jhpieper/marble-run/stl/straight-110.stl

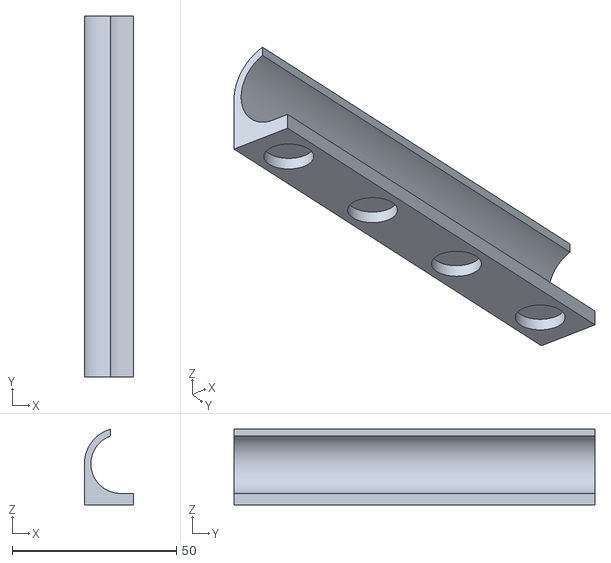
[picture p31: CAD file, 2020-05-29]
stl/straight-110.stl
15.0 x 110.0 x 23.1
