jhpieper/marble-run/stl/wheel-40-6.stl

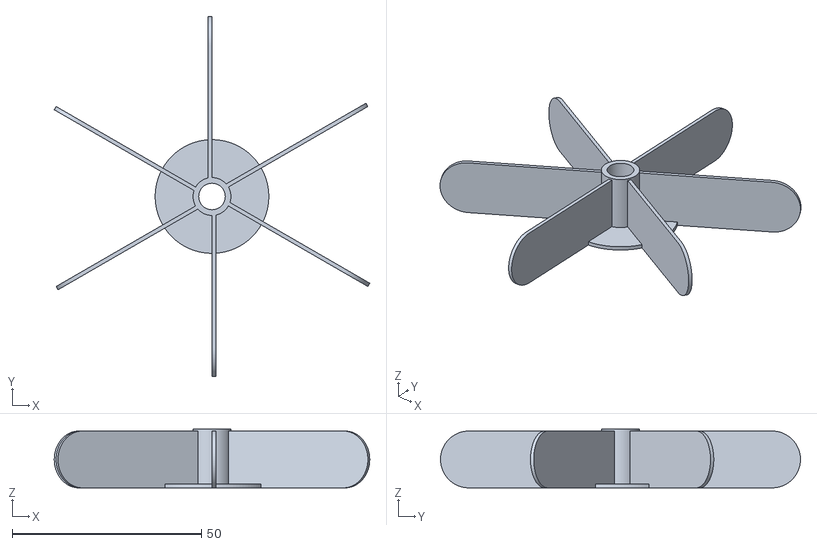
[picture p32: CAD file, 2020-05-29]
stl/wheel-40-6.stl
83.3 x 95.0 x 15.5
