jhpieper/marble-run/stl/pole-base.stl

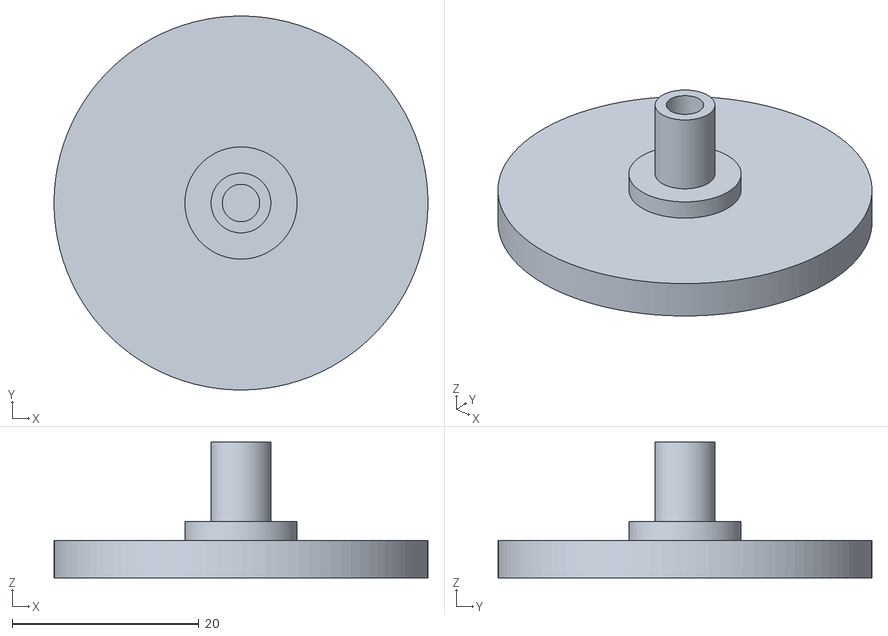
[picture p33: CAD file, 2020-05-29]
stl/pole-base.stl
40.0 x 40.0 x 14.5
