jhpieper/marble-run/stl/wheel-30-5.stl

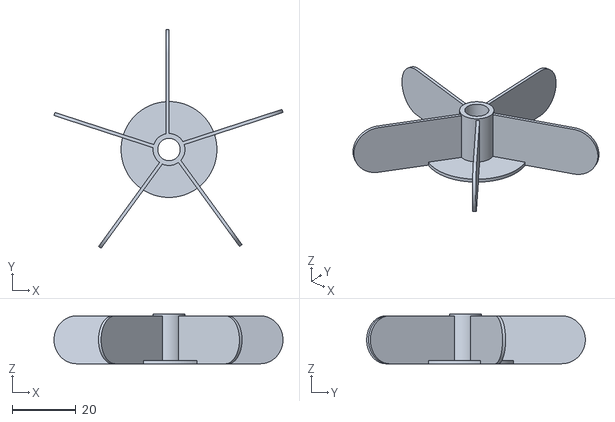
[picture p34: CAD file, 2020-05-29]
stl/wheel-30-5.stl
71.6 x 68.4 x 15.5
