jhpieper/marble-run/stl/wheel-50-7.stl

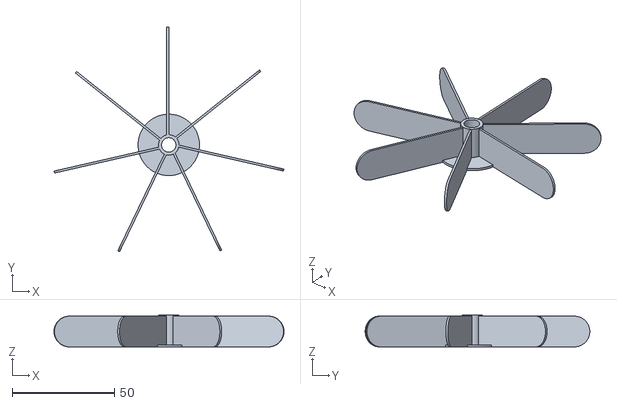
[picture p35: CAD file, 2020-05-29]
stl/wheel-50-7.stl
112.3 x 109.7 x 15.5
