jhpieper/marble-run/stl/wheel-50-9.stl

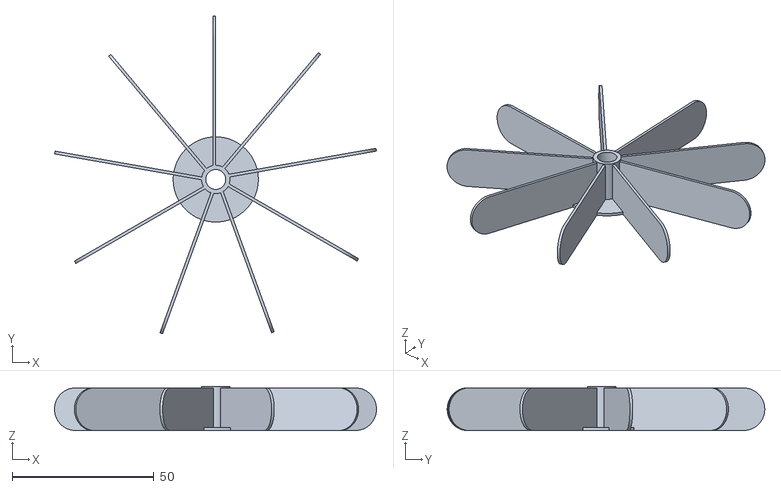
[picture p36: CAD file, 2020-05-29]
stl/wheel-50-9.stl
113.4 x 111.9 x 15.5
