jhpieper/marble-run/stl/straight-170.stl

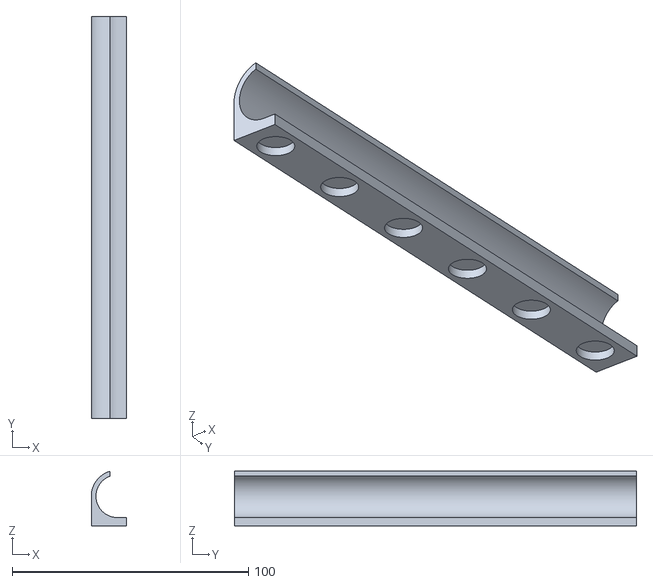
[picture p37: CAD file, 2020-05-29]
stl/straight-170.stl
15.0 x 170.0 x 23.1
