jhpieper/marble-run/stl/wheel-50-5.stl

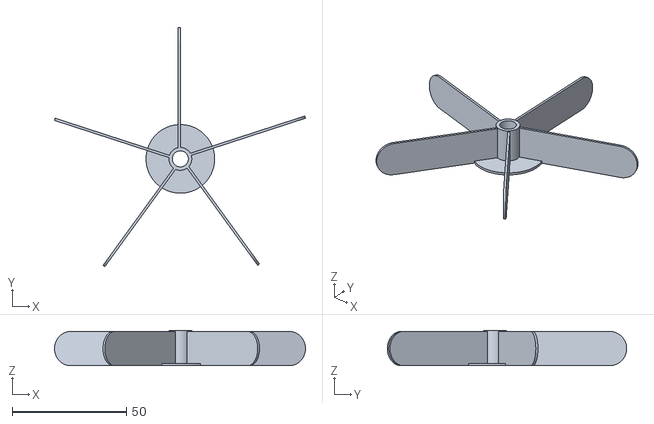
[picture p38: CAD file, 2020-05-29]
stl/wheel-50-5.stl
109.7 x 104.6 x 15.5
