jhpieper/marble-run/stl/wheel-40-5.stl

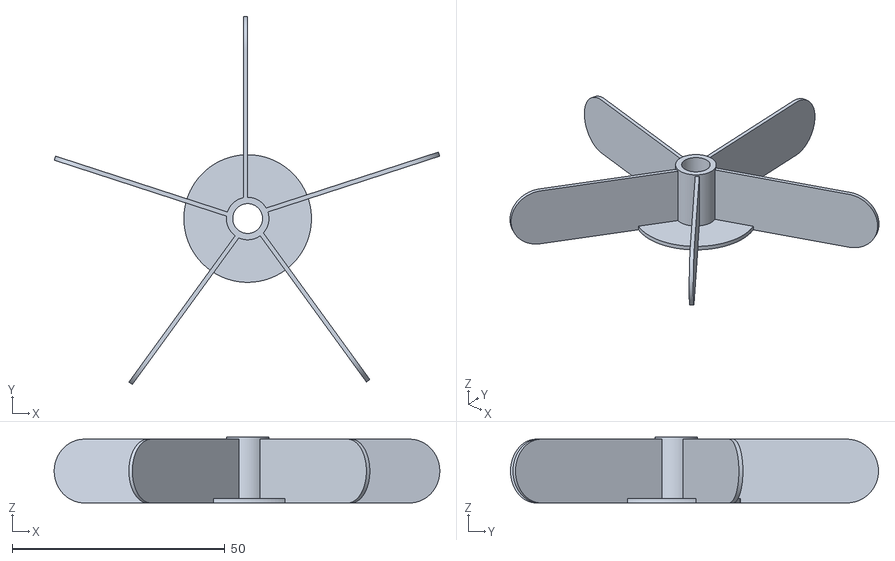
[picture p39: CAD file, 2020-05-29]
stl/wheel-40-5.stl
90.7 x 86.5 x 15.5
