jhpieper/marble-run/stl/lock-star.stl

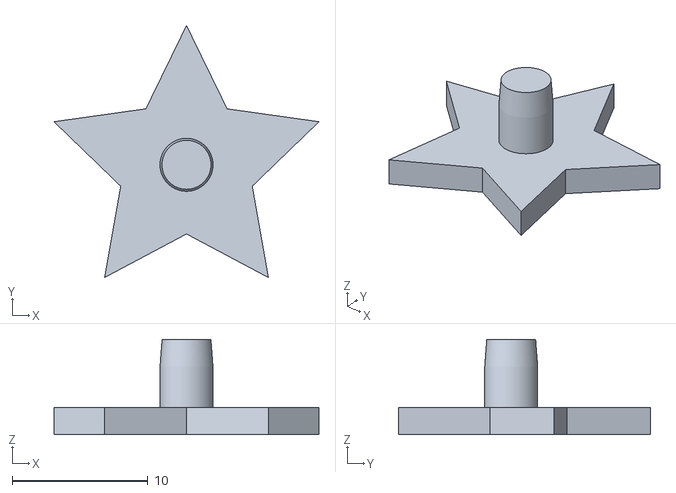
[picture p40: CAD file, 2020-05-29]
stl/lock-star.stl
19.5 x 18.5 x 7.00
