jhpieper/marble-run/stl/straight-80.stl

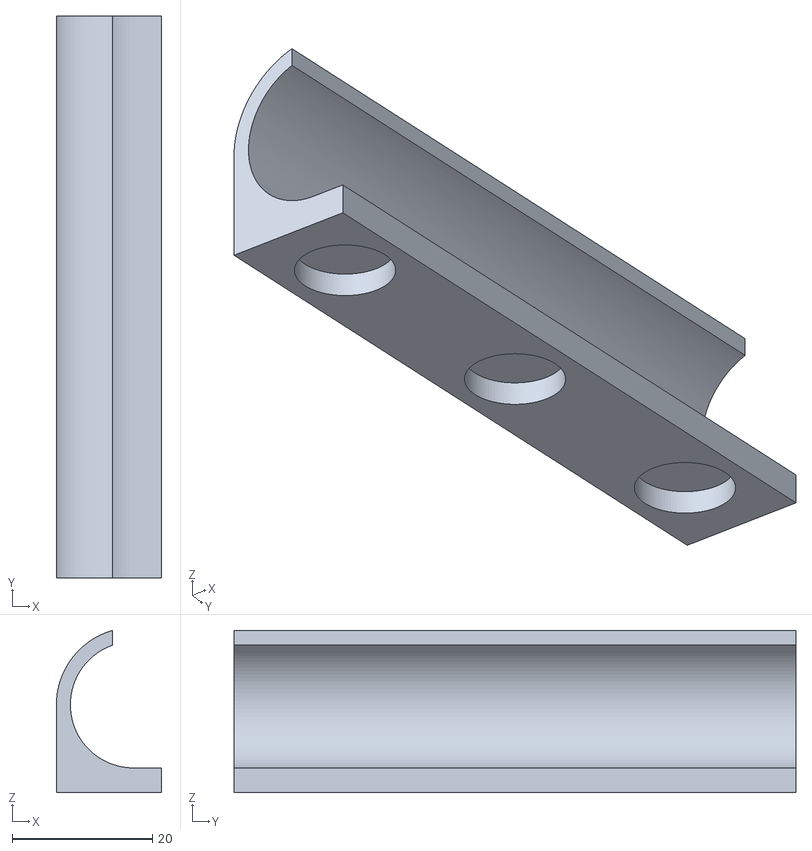
[picture p41: CAD file, 2020-05-29]
stl/straight-80.stl
15.0 x 80.0 x 23.1
