jhpieper/marble-run/stl/straight-200.stl

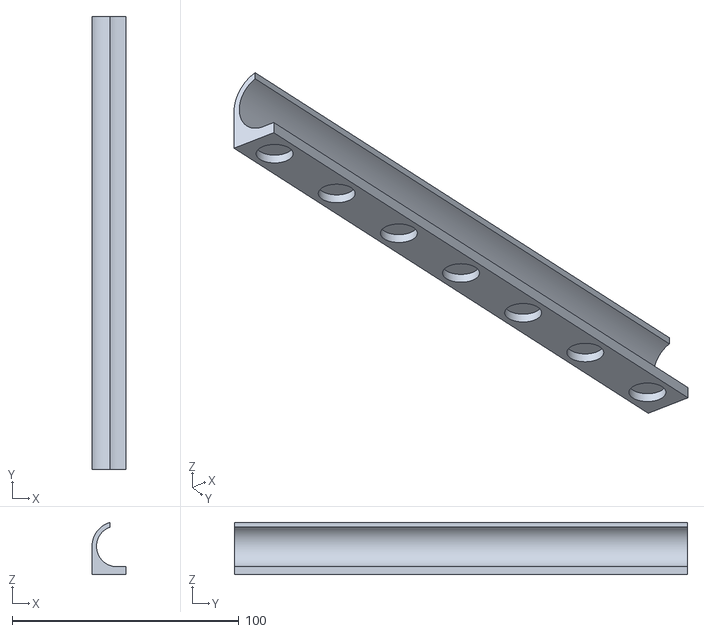
[picture p42: CAD file, 2020-05-29]
stl/straight-200.stl
15.0 x 200.0 x 23.1
