jhpieper/marble-run/stl/drop-left.stl

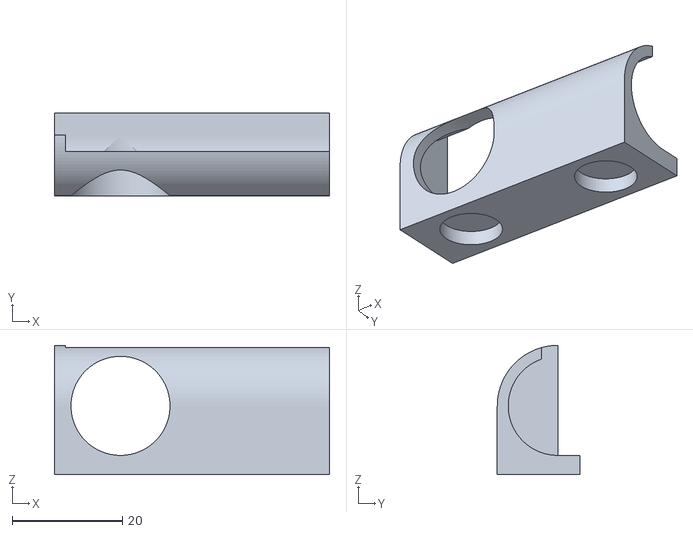
[picture p43: CAD file, 2020-05-29]
stl/drop-left.stl
50.0 x 15.0 x 23.5
