jhpieper/marble-run/stl/wheel-50-6.stl

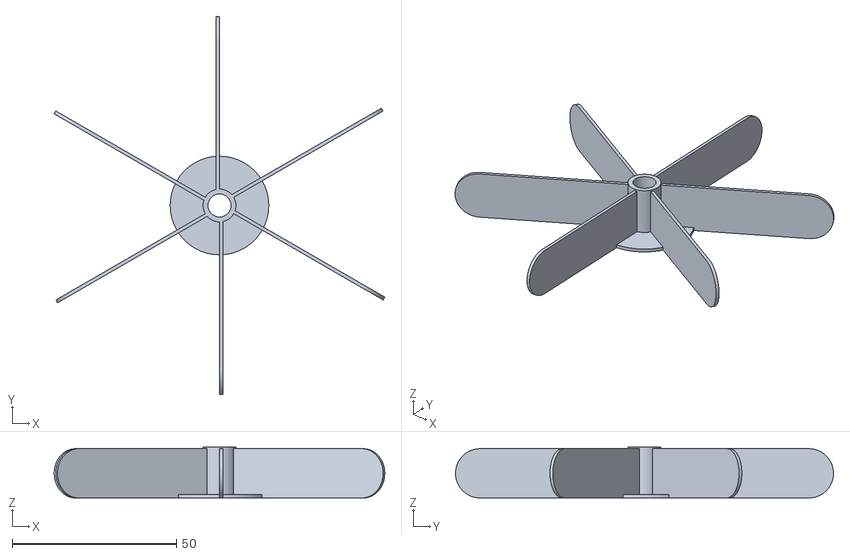
[picture p44: CAD file, 2020-05-29]
stl/wheel-50-6.stl
100.6 x 115.0 x 15.5
