jhpieper/marble-run/stl/wheel-50-2.stl

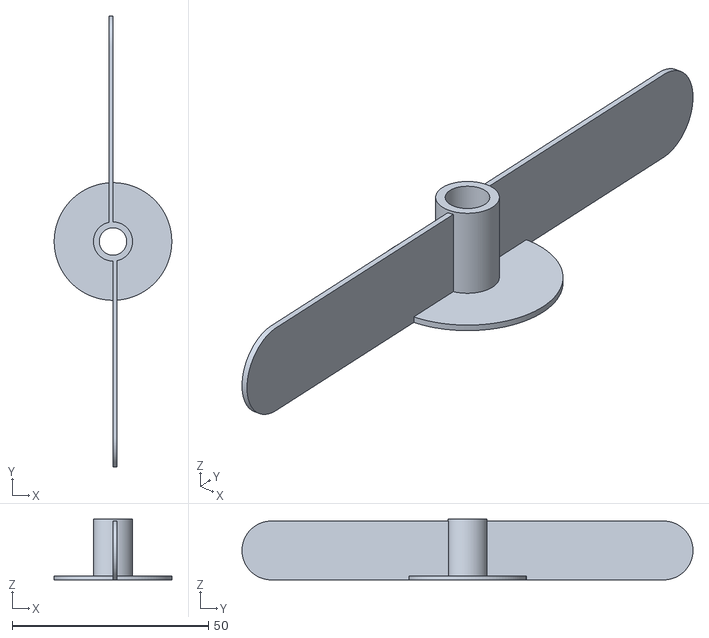
[picture p45: CAD file, 2020-05-29]
stl/wheel-50-2.stl
30.0 x 115.0 x 15.5
