jhpieper/marble-run/stl/wheel-30-6.stl

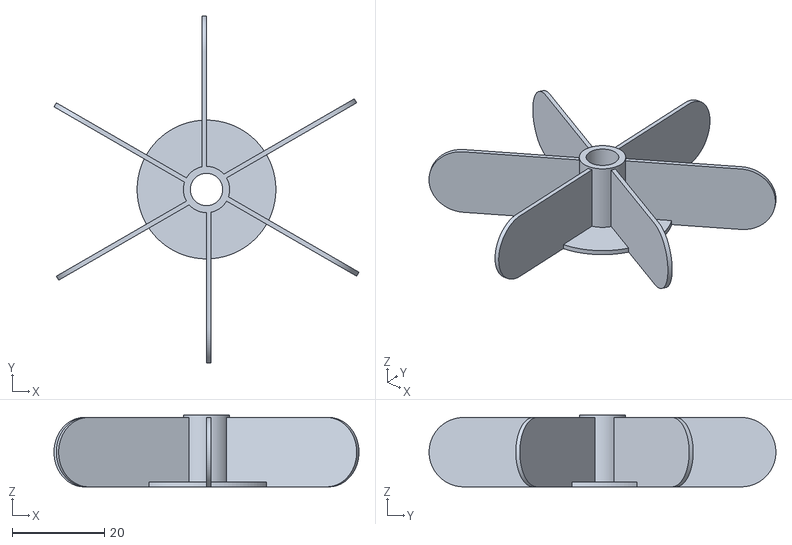
[picture p46: CAD file, 2020-05-29]
stl/wheel-30-6.stl
66.0 x 75.0 x 15.5
