jhpieper/marble-run/stl/pole-right.stl

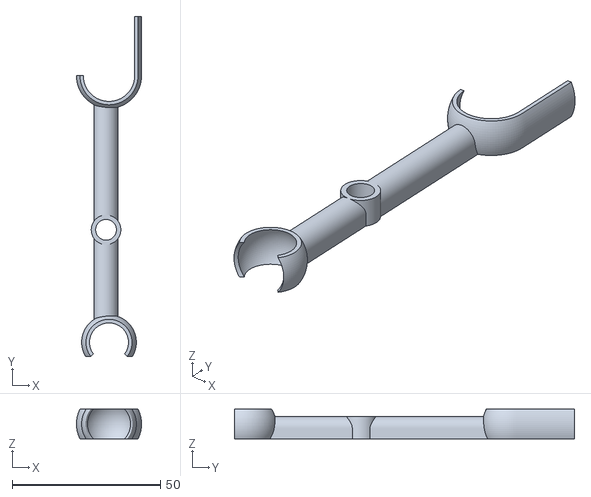
[picture p47: CAD file, 2020-05-29]
stl/pole-right.stl
22.0 x 114.8 x 10.0
