jhpieper/marble-run/stl/wheel-40-9.stl

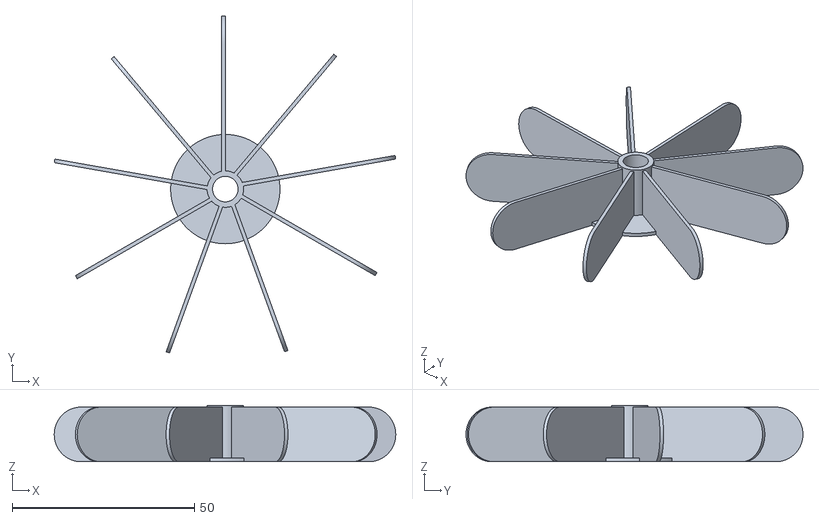
[picture p48: CAD file, 2020-05-29]
stl/wheel-40-9.stl
93.7 x 92.5 x 15.5
