jhpieper/marble-run/stl/wheel-40-2.stl

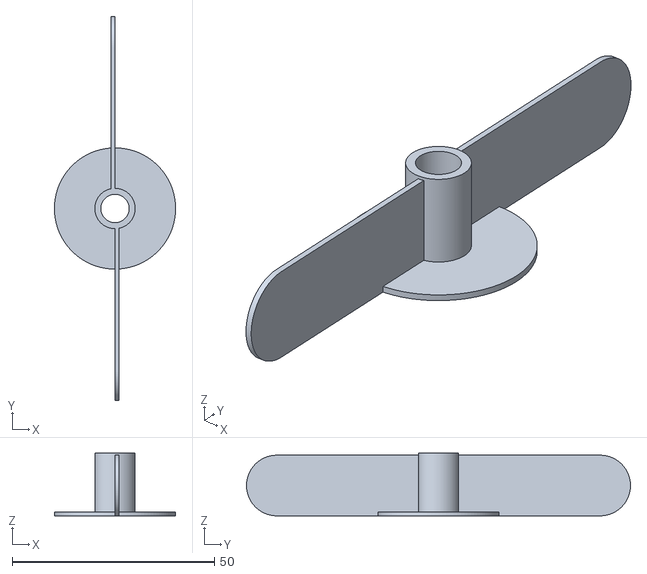
[picture p49: CAD file, 2020-05-29]
stl/wheel-40-2.stl
30.0 x 95.0 x 15.5
