jhpieper/marble-run/stl/wheel-40-7.stl

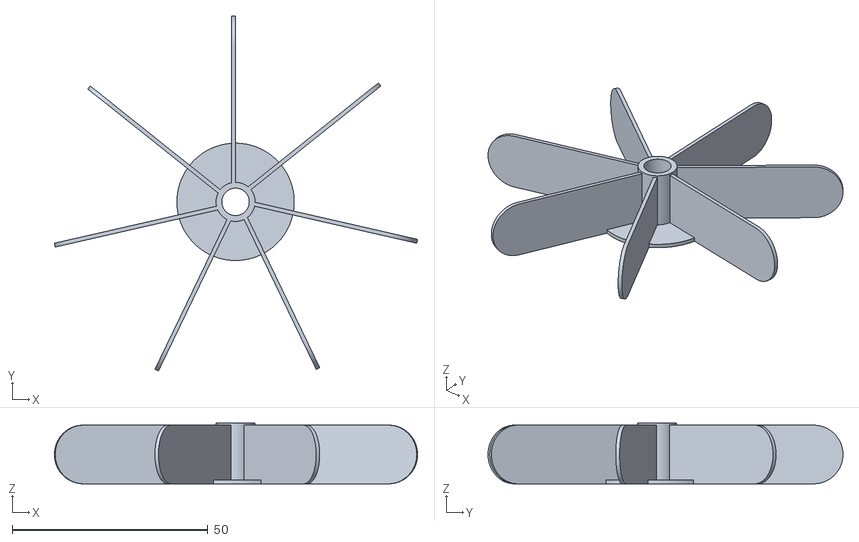
[picture p50: CAD file, 2020-05-29]
stl/wheel-40-7.stl
92.8 x 90.7 x 15.5
