jhpieper/marble-run/stl/straight-140.stl

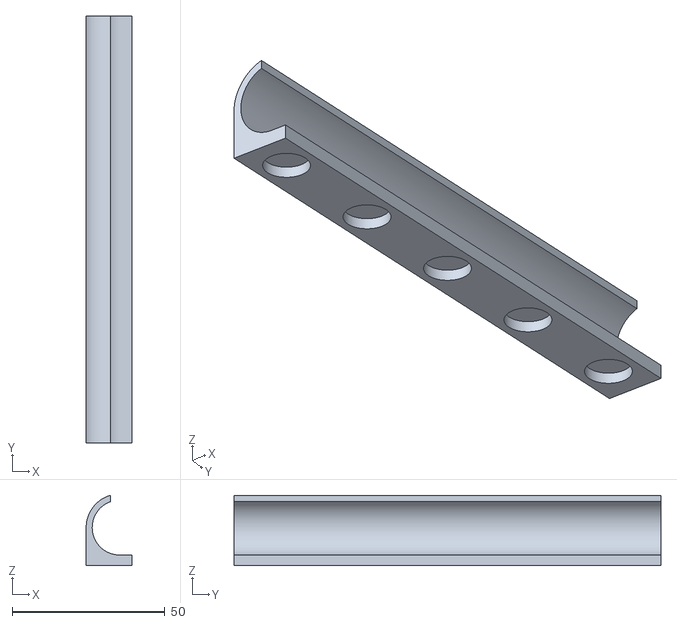
[picture p51: CAD file, 2020-05-29]
stl/straight-140.stl
15.0 x 140.0 x 23.1
