jhpieper/marble-run/stl/lock-round.stl

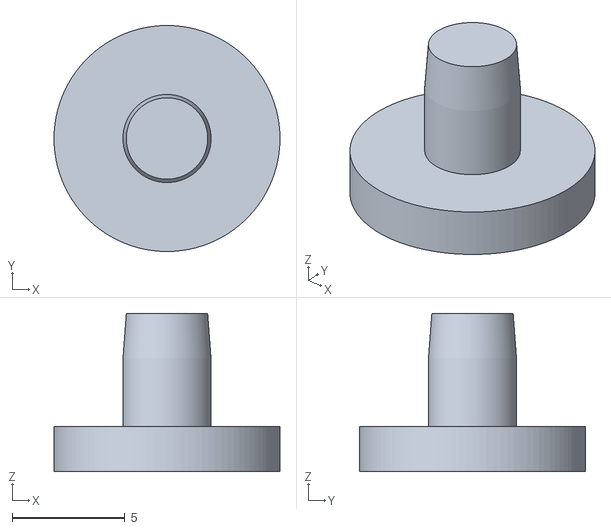
[picture p52: CAD file, 2020-05-29]
stl/lock-round.stl
10.0 x 10.0 x 7.00
