jhpieper/marble-run/stl/straight-50.stl

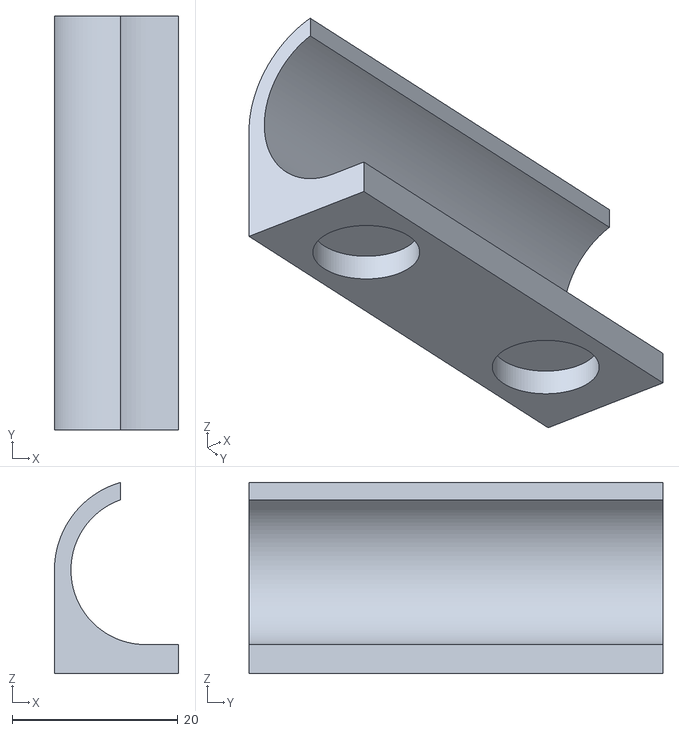
[picture p53: CAD file, 2020-05-29]
stl/straight-50.stl
15.0 x 50.0 x 23.1
