jhpieper/marble-run/stl/wheel-base.stl

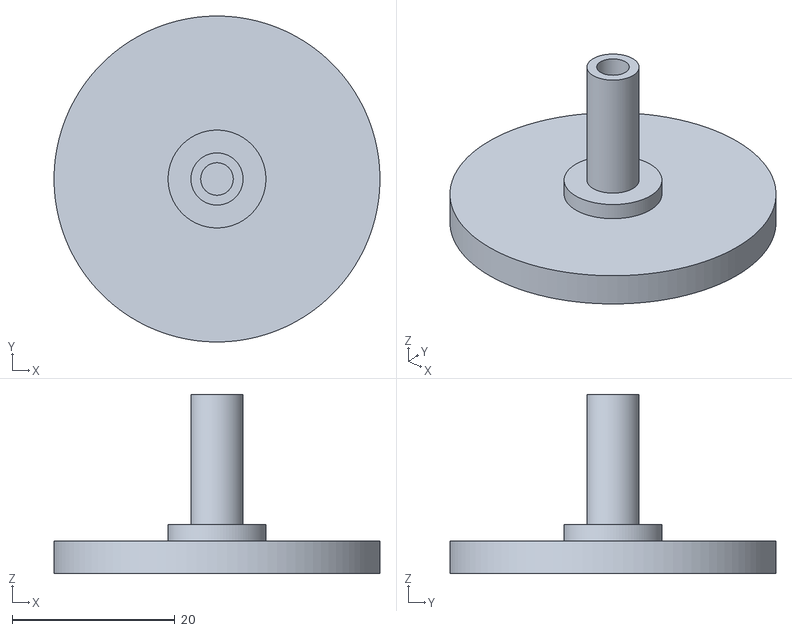
[picture p54: CAD file, 2020-05-29]
stl/wheel-base.stl
40.0 x 40.0 x 22.0
